handiko/VHF-LNA/Pics/IMG_20181112_010419.jpg

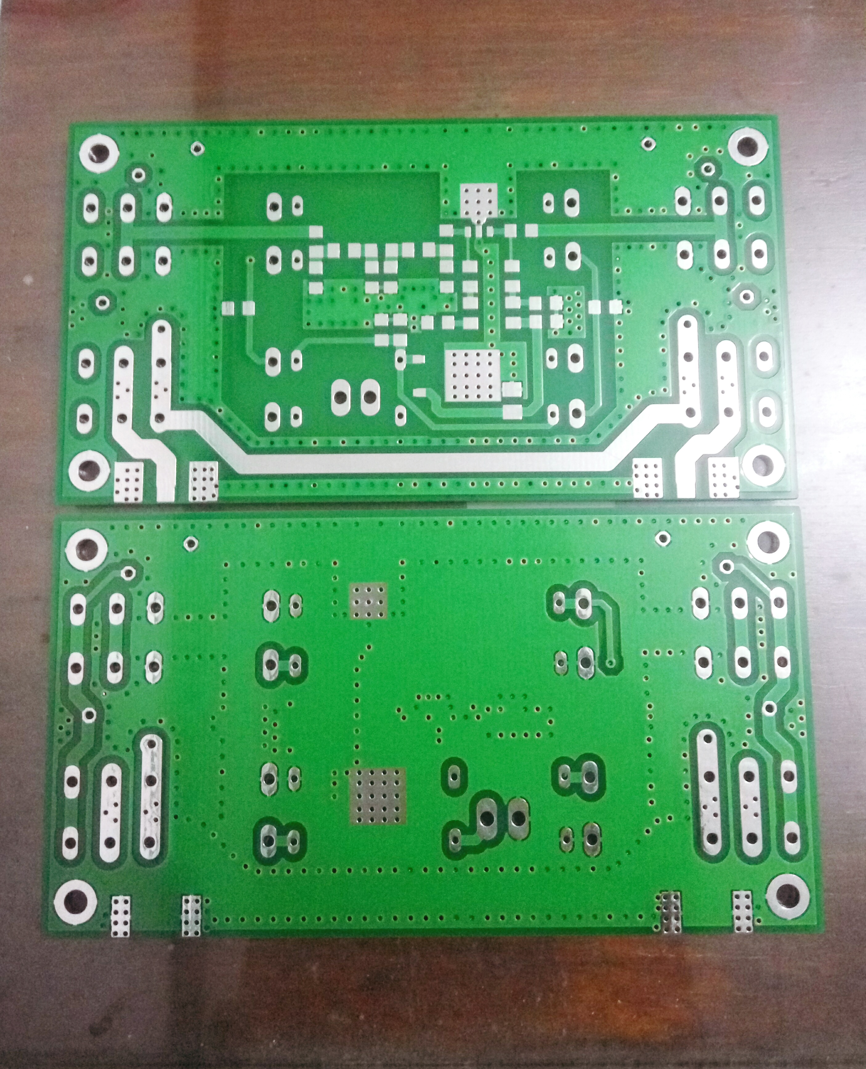
Pics/IMG_20181112_010419.jpg
