handiko/VHF-LNA/Pics/IMG_20181201_112747.jpg

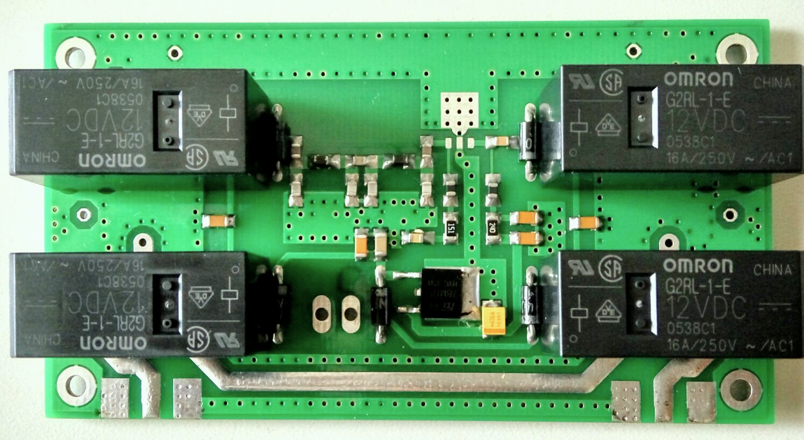
Pics/IMG_20181201_112747.jpg
